victor1533111/SorterBot/CODIGO/Imagenes/angulo.jpg

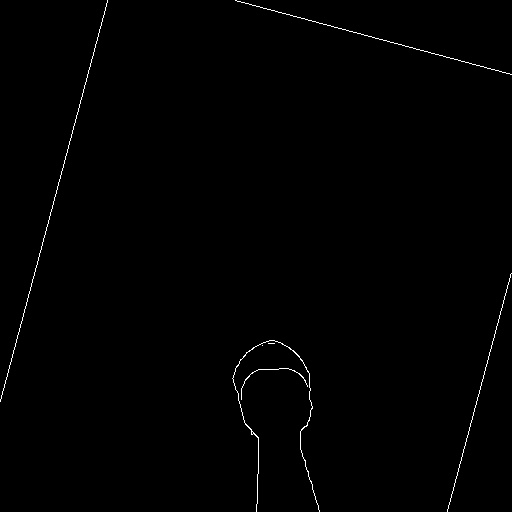
CODIGO/Imagenes/angulo.jpg
