victor1533111/SorterBot/CODIGO/Imagenes/contornos.jpg

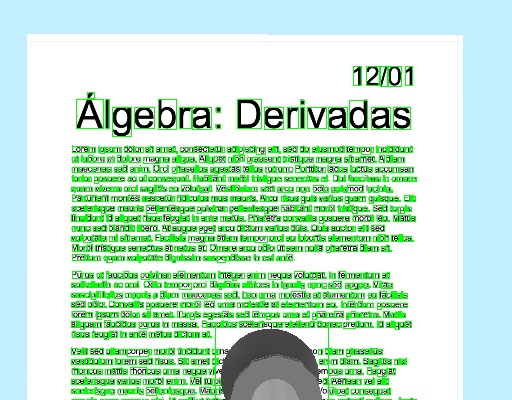
CODIGO/Imagenes/contornos.jpg
