victor1533111/SorterBot/CODIGO/Imagenes/foto.jpg

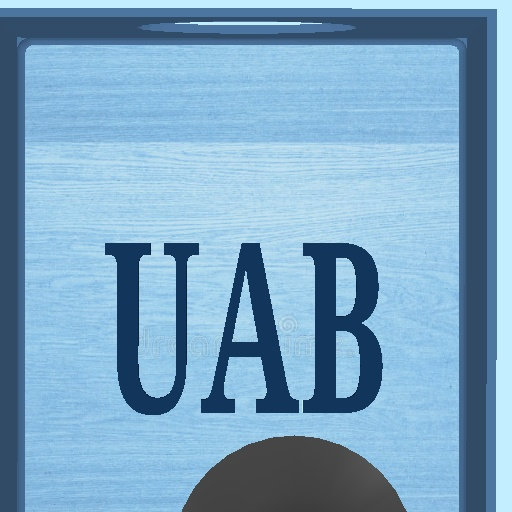
CODIGO/Imagenes/foto.jpg
