victor1533111/SorterBot/CODIGO/Imagenes/foto_titulo.jpg

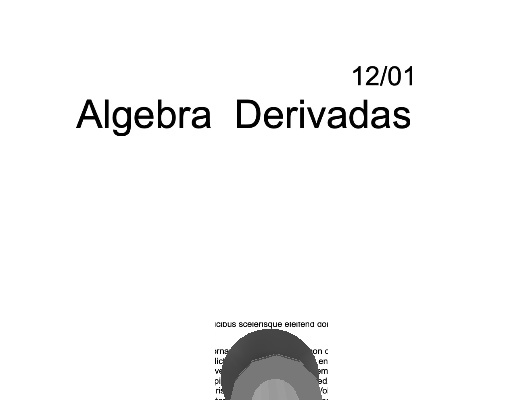
CODIGO/Imagenes/foto_titulo.jpg
