victor1533111/SorterBot/COMPONENTES/TEXTURAS/Colores/0c4315f0d65723472475a9147a5b7592.jpg

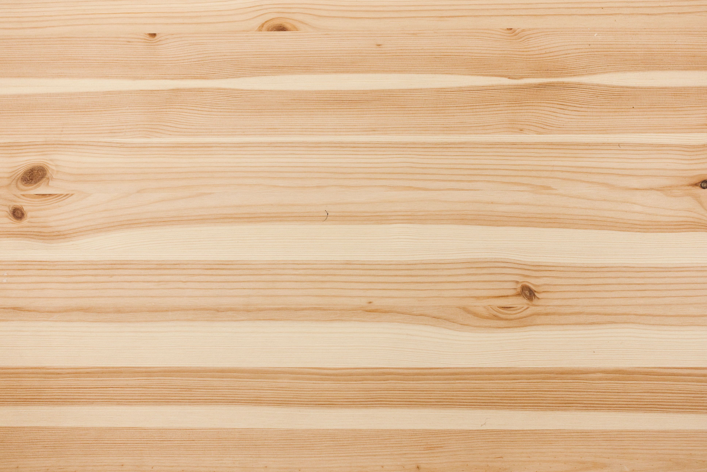
COMPONENTES/TEXTURAS/Colores/0c4315f0d65723472475a9147a5b7592.jpg
