victor1533111/SorterBot/COMPONENTES/TEXTURAS/Colores/40899414-suelo-de-parqué-gris-textura-de-madera-con-tablones-horizontales.jpg

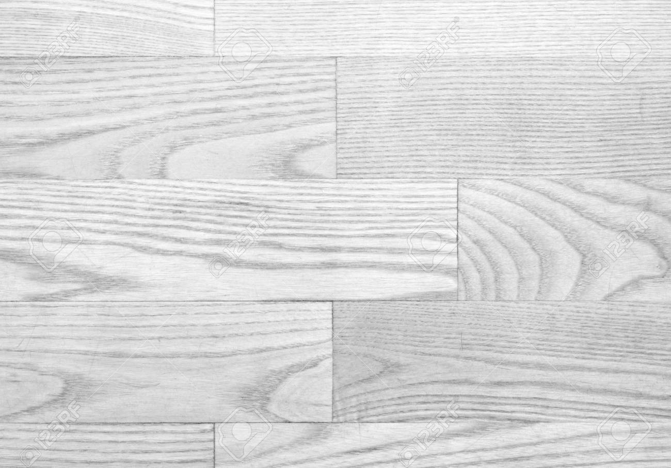
COMPONENTES/TEXTURAS/Colores/40899414-suelo-de-parqué-gris-textura-de-madera-con-tablones-horizontales.jpg
