victor1533111/SorterBot/COMPONENTES/TEXTURAS/Colores/cropped-uab.jpg

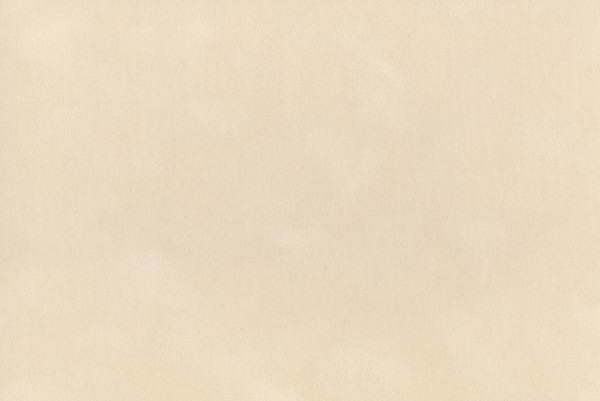
COMPONENTES/TEXTURAS/Colores/cropped-uab.jpg
