victor1533111/SorterBot/COMPONENTES/TEXTURAS/Colores/depositphotos_195791748-stock-photo-dark-brown-scratched-wooden-cutting.png

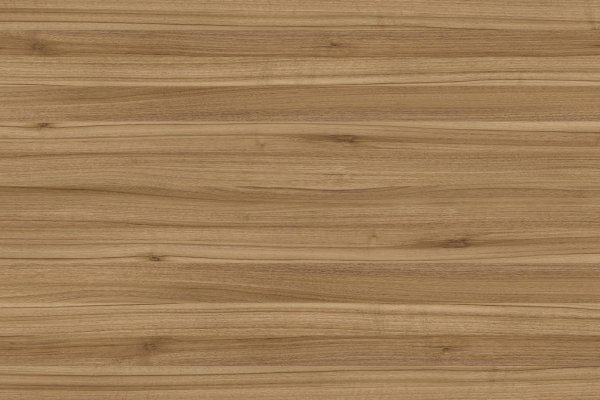
COMPONENTES/TEXTURAS/Colores/depositphotos_195791748-stock-photo-dark-brown-scratched-wooden-cutting.png
