victor1533111/SorterBot/COMPONENTES/TEXTURAS/Colores/fondo-de-textura-suelo-laminado-blanco-inoxidable-parqué-madera-gris-pulida-168998200.jpg

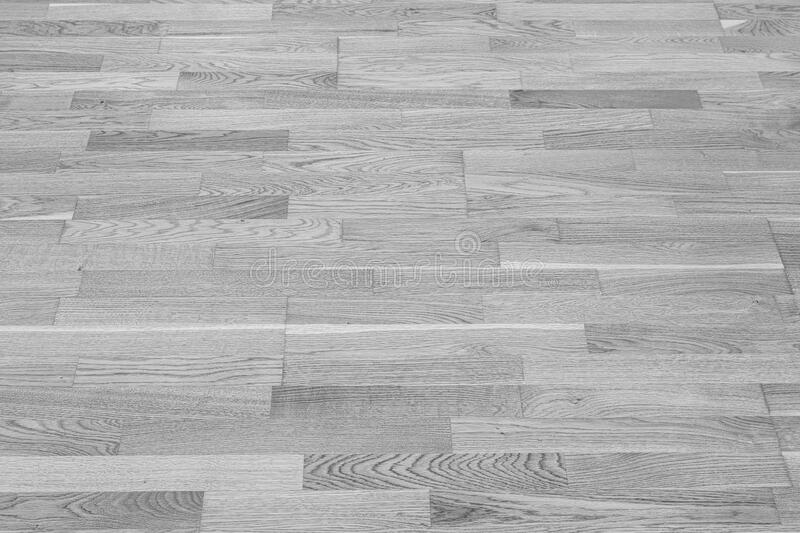
COMPONENTES/TEXTURAS/Colores/fondo-de-textura-suelo-laminado-blanco-inoxidable-parqué-madera-gris-pulida-168998200.jpg
