victor1533111/SorterBot/COMPONENTES/TEXTURAS/Colores/fp_eiche_no1102_1199010840_sb_of1223_plan_191213_1.jpg

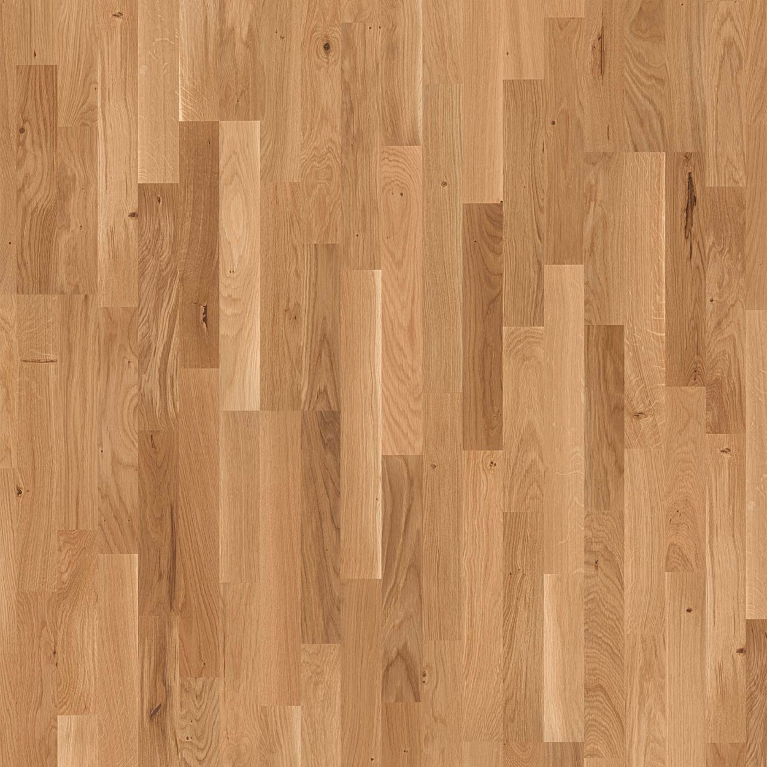
COMPONENTES/TEXTURAS/Colores/fp_eiche_no1102_1199010840_sb_of1223_plan_191213_1.jpg
