victor1533111/SorterBot/COMPONENTES/TEXTURAS/Colores/imu1861_1.jpg

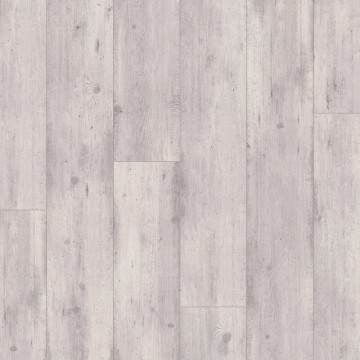
COMPONENTES/TEXTURAS/Colores/imu1861_1.jpg
