victor1533111/SorterBot/COMPONENTES/TEXTURAS/Colores/parquet.png

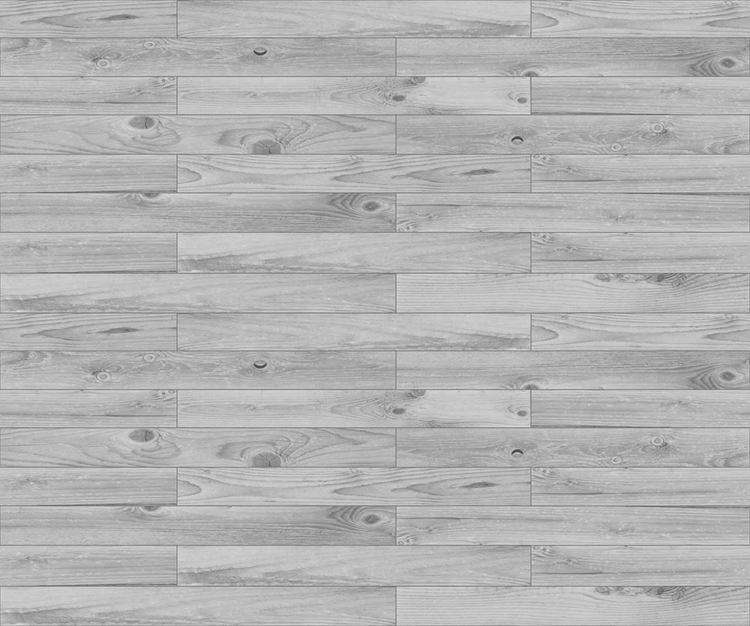
COMPONENTES/TEXTURAS/Colores/parquet.png
