victor1533111/SorterBot/COMPONENTES/TEXTURAS/Colores/wood-texture-table-top-surface-background-natural-pattern-top-view-wood-texture-table-top-surface-ba.png

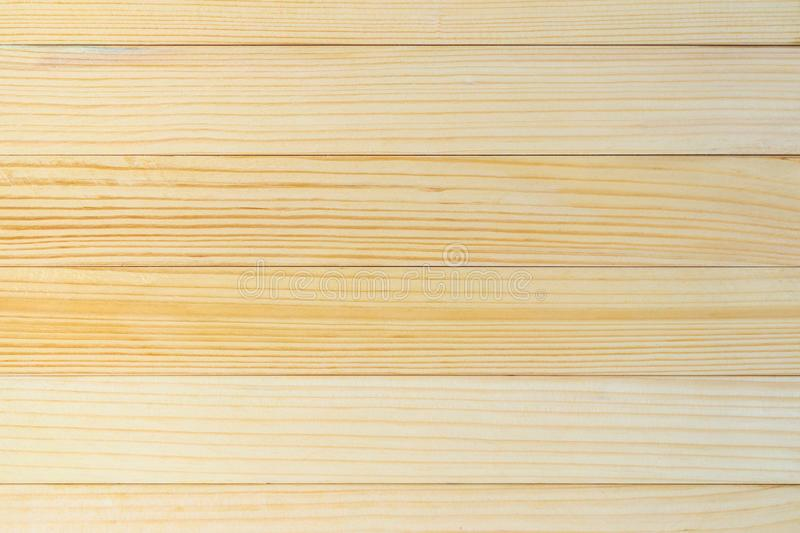
COMPONENTES/TEXTURAS/Colores/wood-texture-table-top-surface-background-natural-pattern-top-view-wood-texture-table-top-surface-ba.png
