victor1533111/SorterBot/COMPONENTES/TEXTURAS/Hojas/AC_Processador.jpg

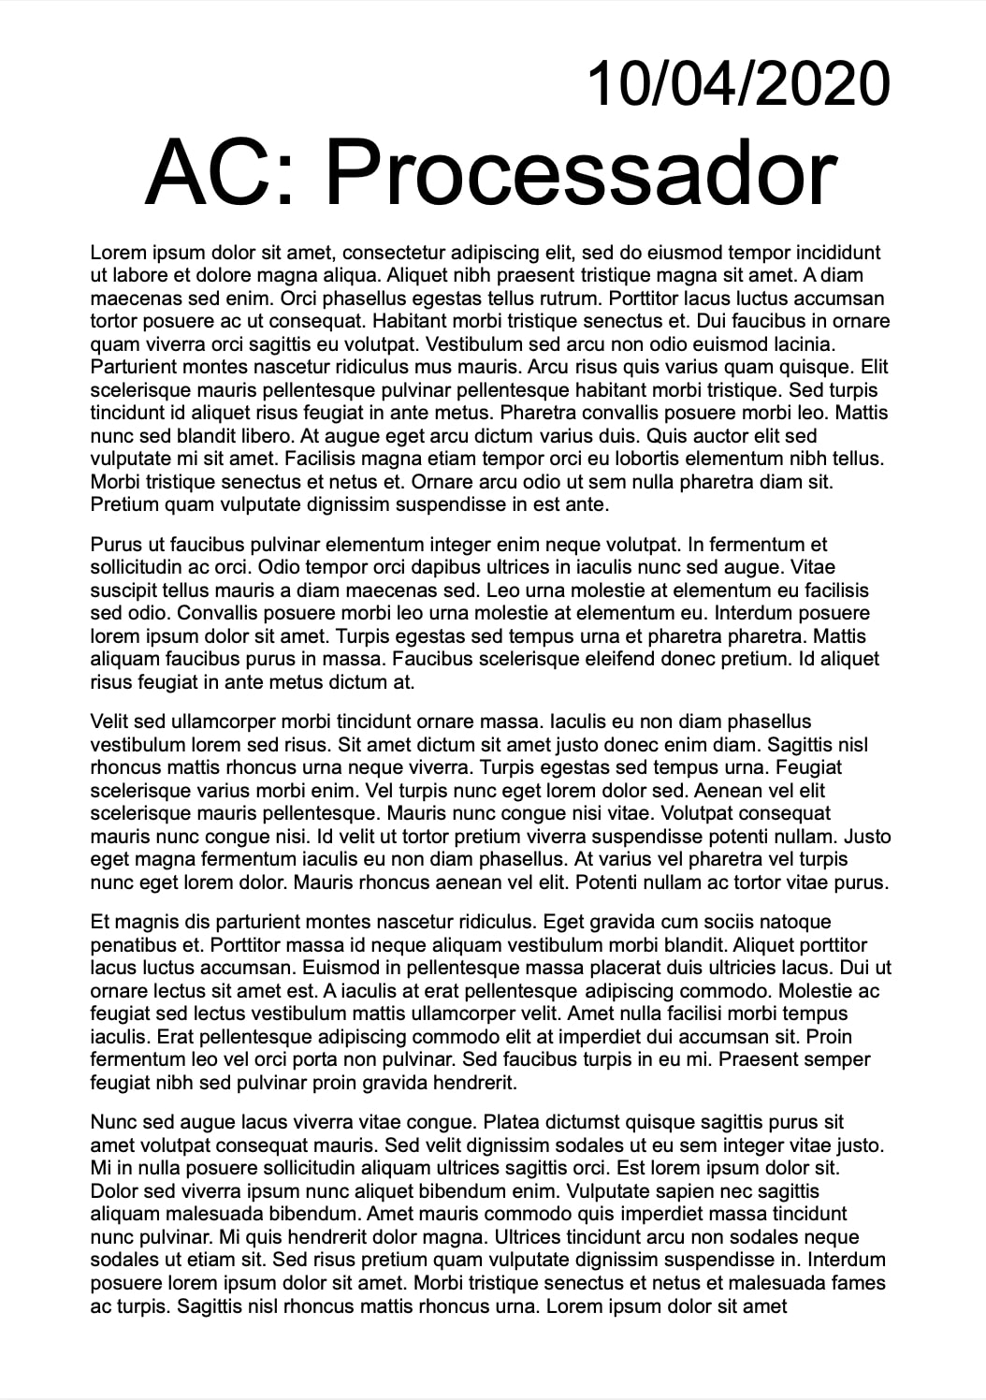
COMPONENTES/TEXTURAS/Hojas/AC_Processador.jpg
