victor1533111/SorterBot/COMPONENTES/TEXTURAS/Hojas/AC_SIMD.jpg

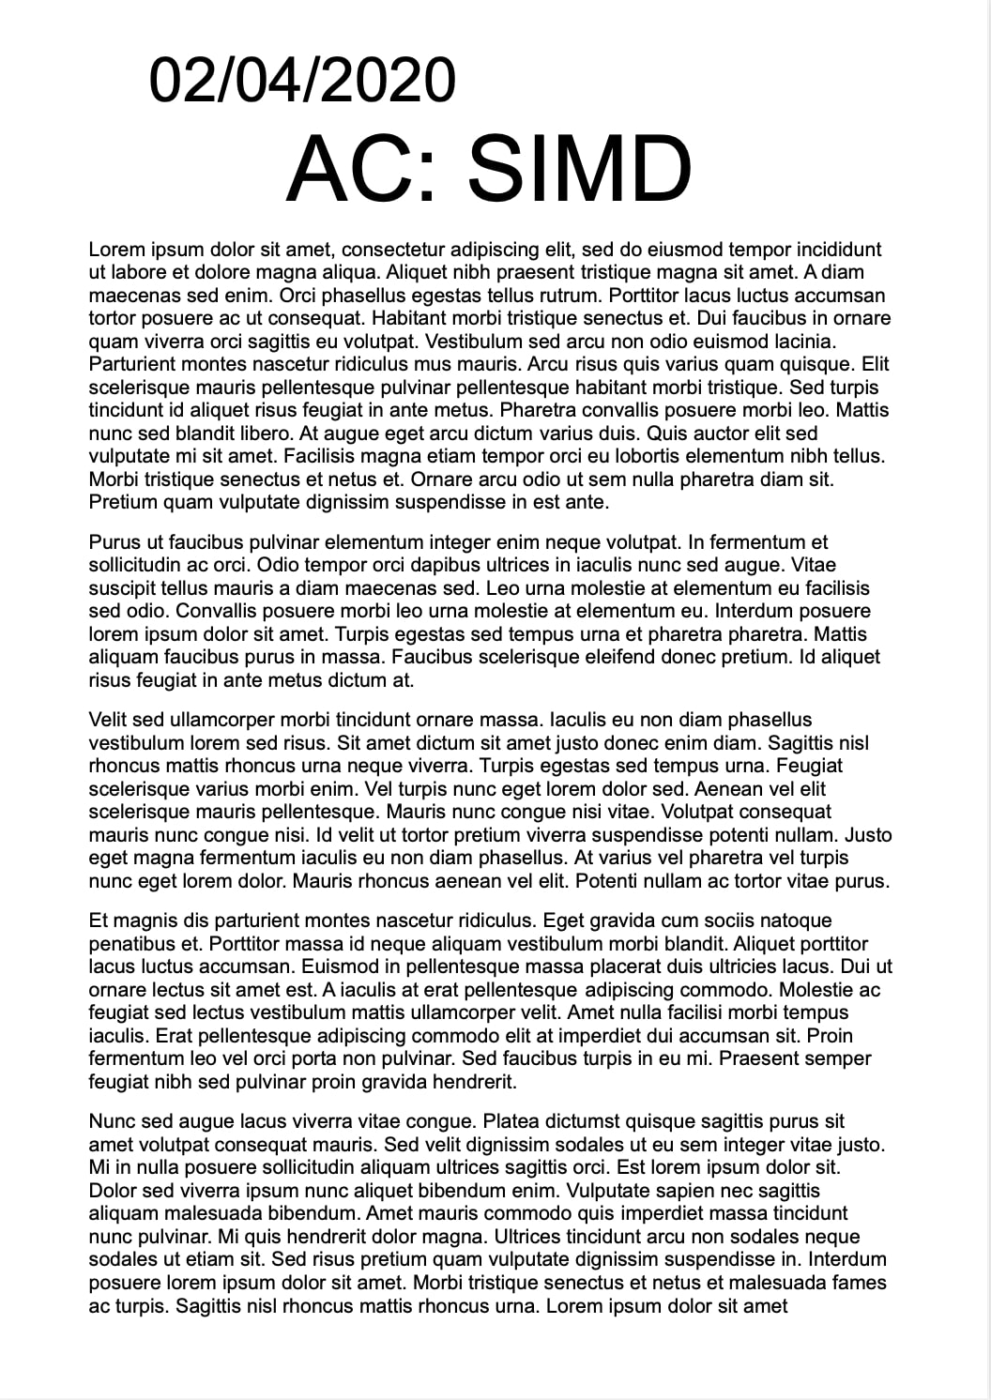
COMPONENTES/TEXTURAS/Hojas/AC_SIMD.jpg
