victor1533111/SorterBot/COMPONENTES/TEXTURAS/Hojas/Algebra_Derivadas.jpg

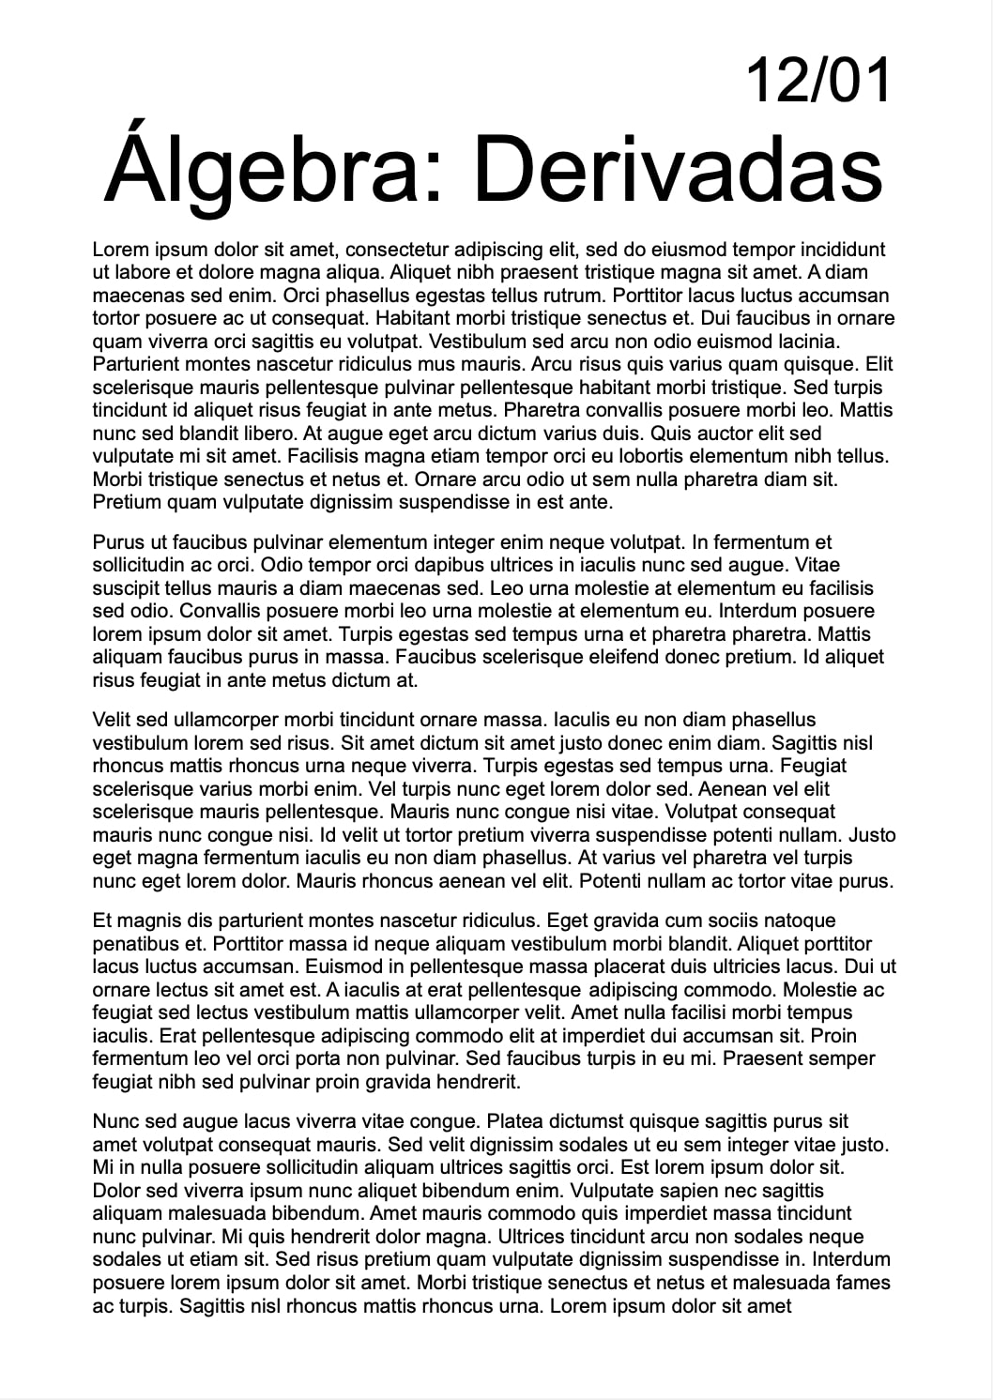
COMPONENTES/TEXTURAS/Hojas/Algebra_Derivadas.jpg
