victor1533111/SorterBot/COMPONENTES/TEXTURAS/Hojas/Algebra_Integrales.jpg

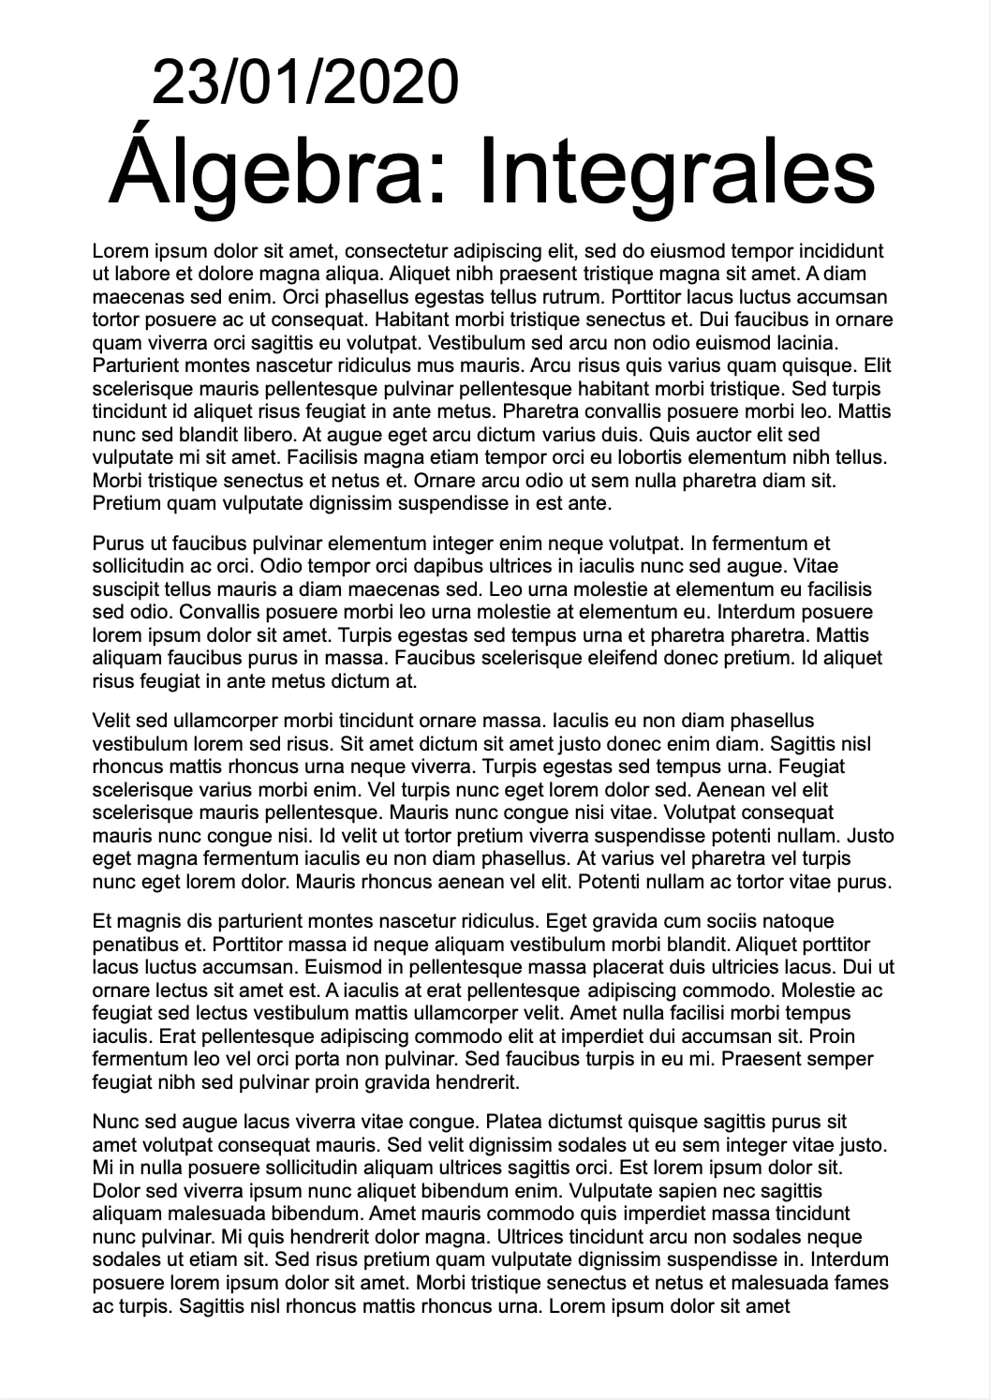
COMPONENTES/TEXTURAS/Hojas/Algebra_Integrales.jpg
