victor1533111/SorterBot/COMPONENTES/TEXTURAS/Hojas/Algebra_Matrices.jpg

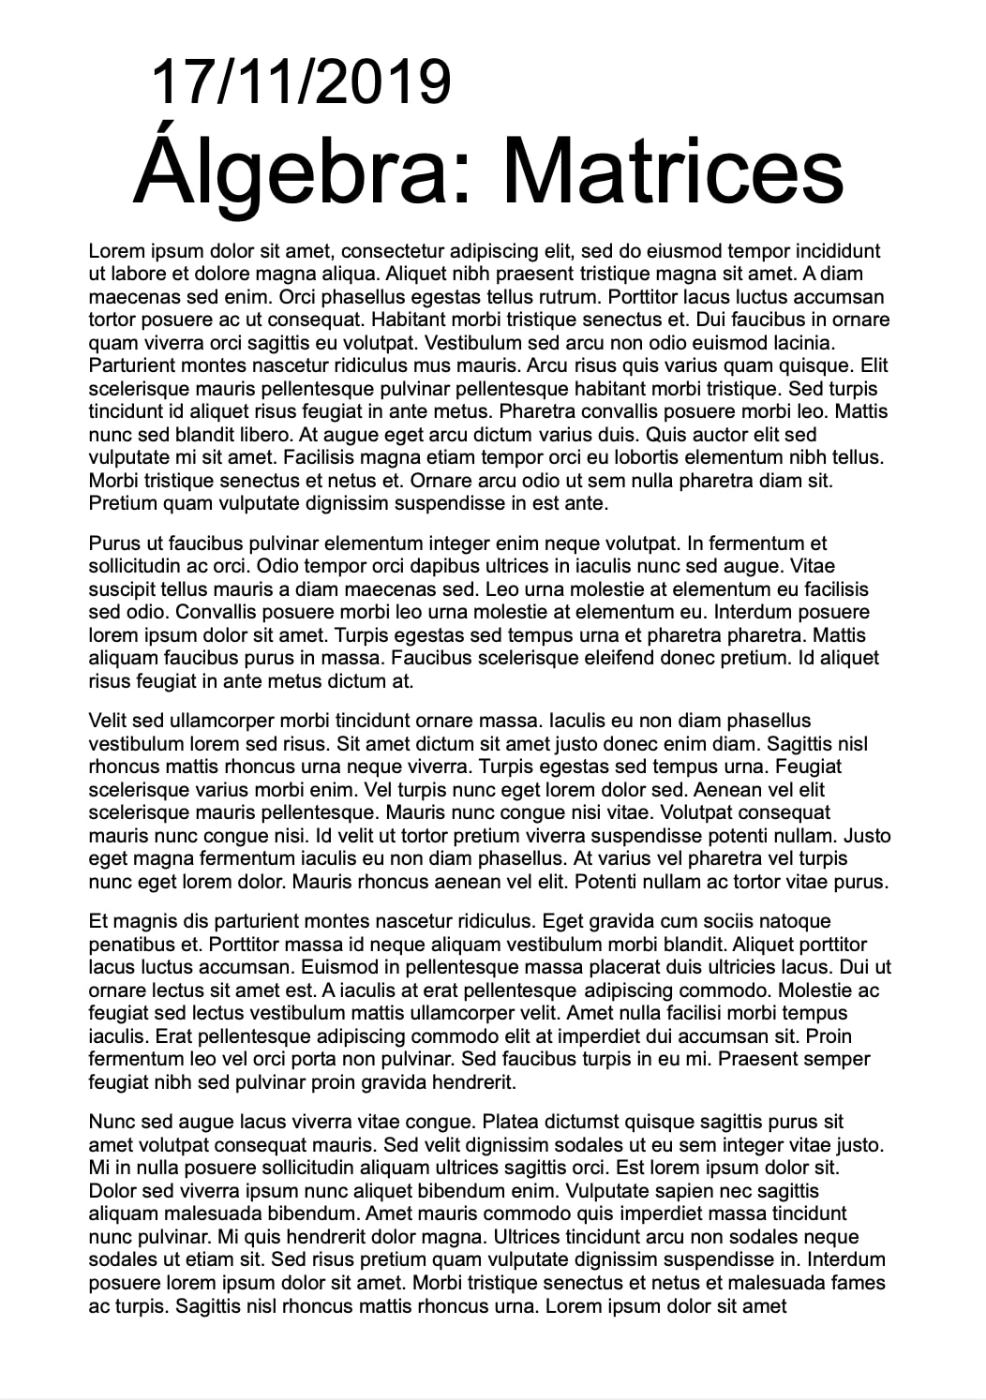
COMPONENTES/TEXTURAS/Hojas/Algebra_Matrices.jpg
