victor1533111/SorterBot/COMPONENTES/TEXTURAS/Hojas/Robotica_Algoritmo.jpg

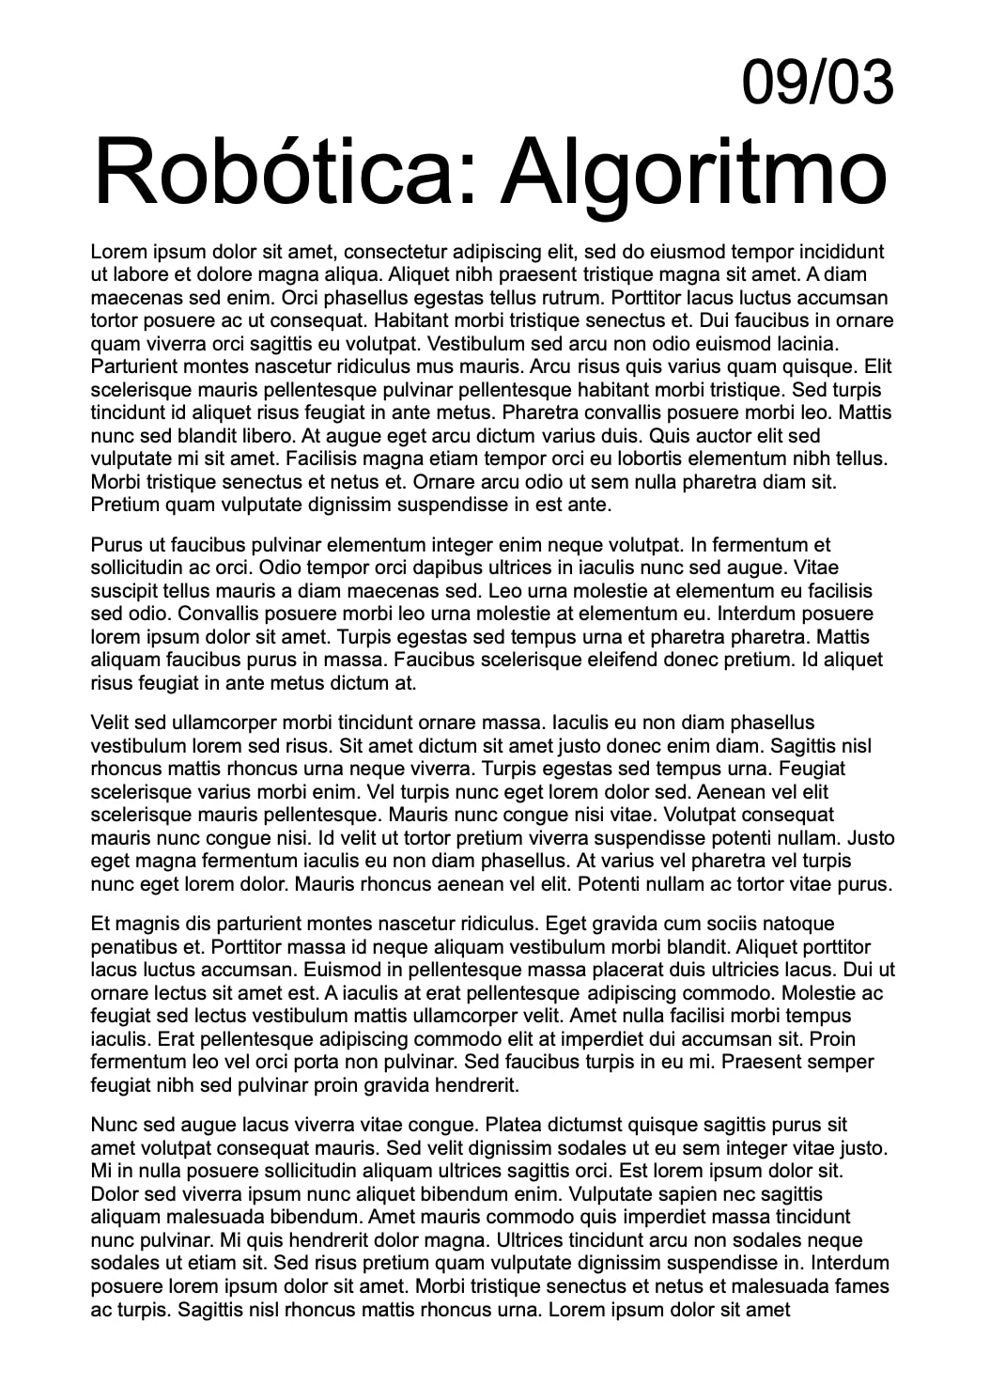
COMPONENTES/TEXTURAS/Hojas/Robotica_Algoritmo.jpg
