victor1533111/SorterBot/COMPONENTES/TEXTURAS/Hojas/Robotica_Cinematica.jpg

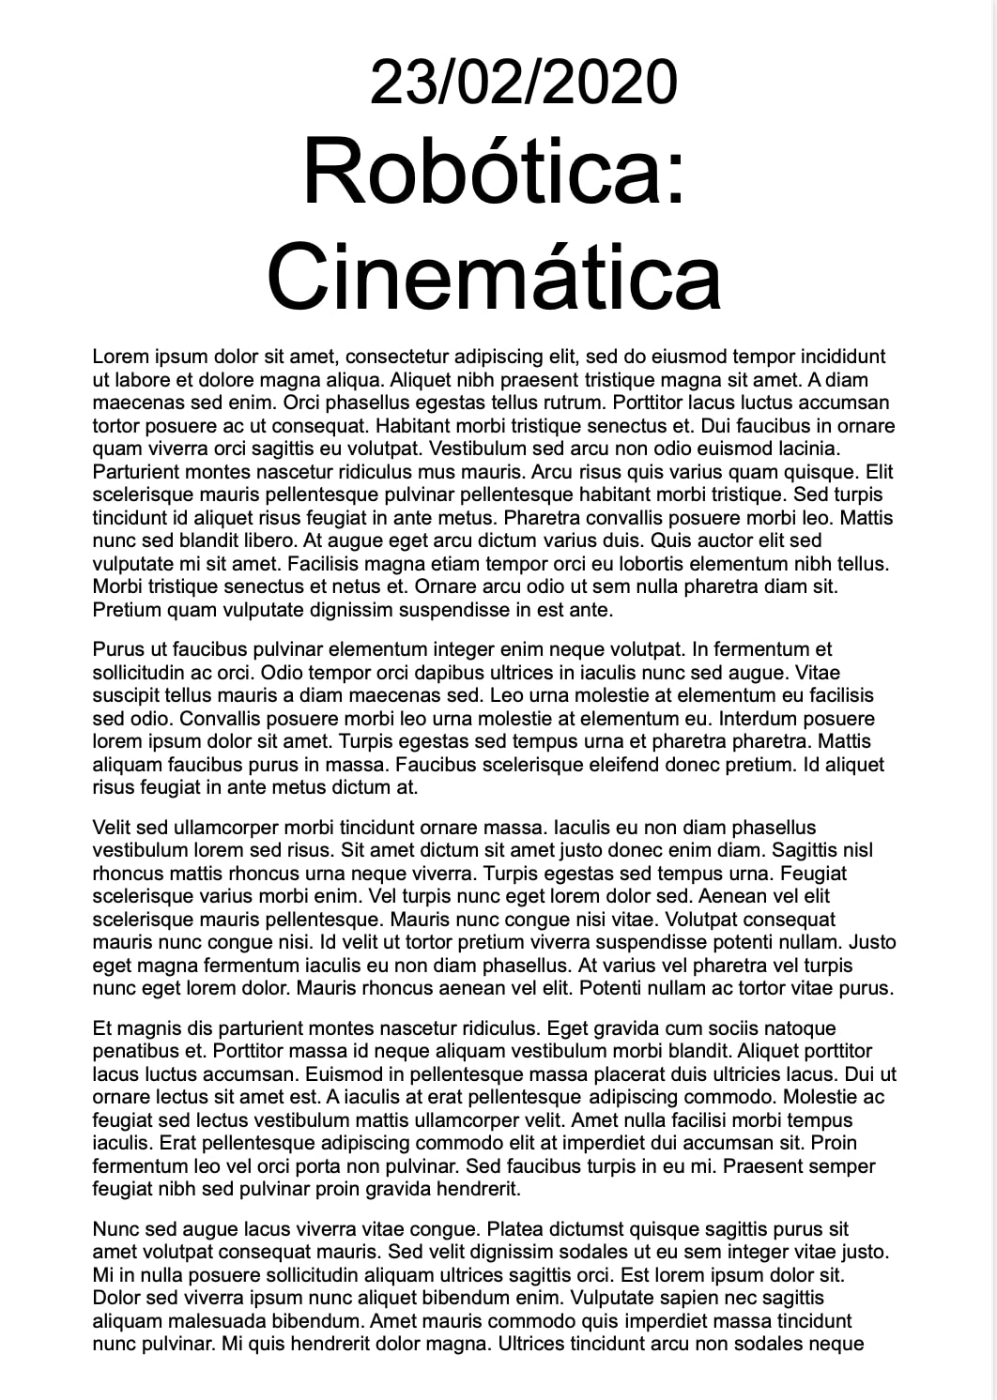
COMPONENTES/TEXTURAS/Hojas/Robotica_Cinematica.jpg
