victor1533111/SorterBot/COMPONENTES/TEXTURAS/Hojas/SO_Linux.jpg

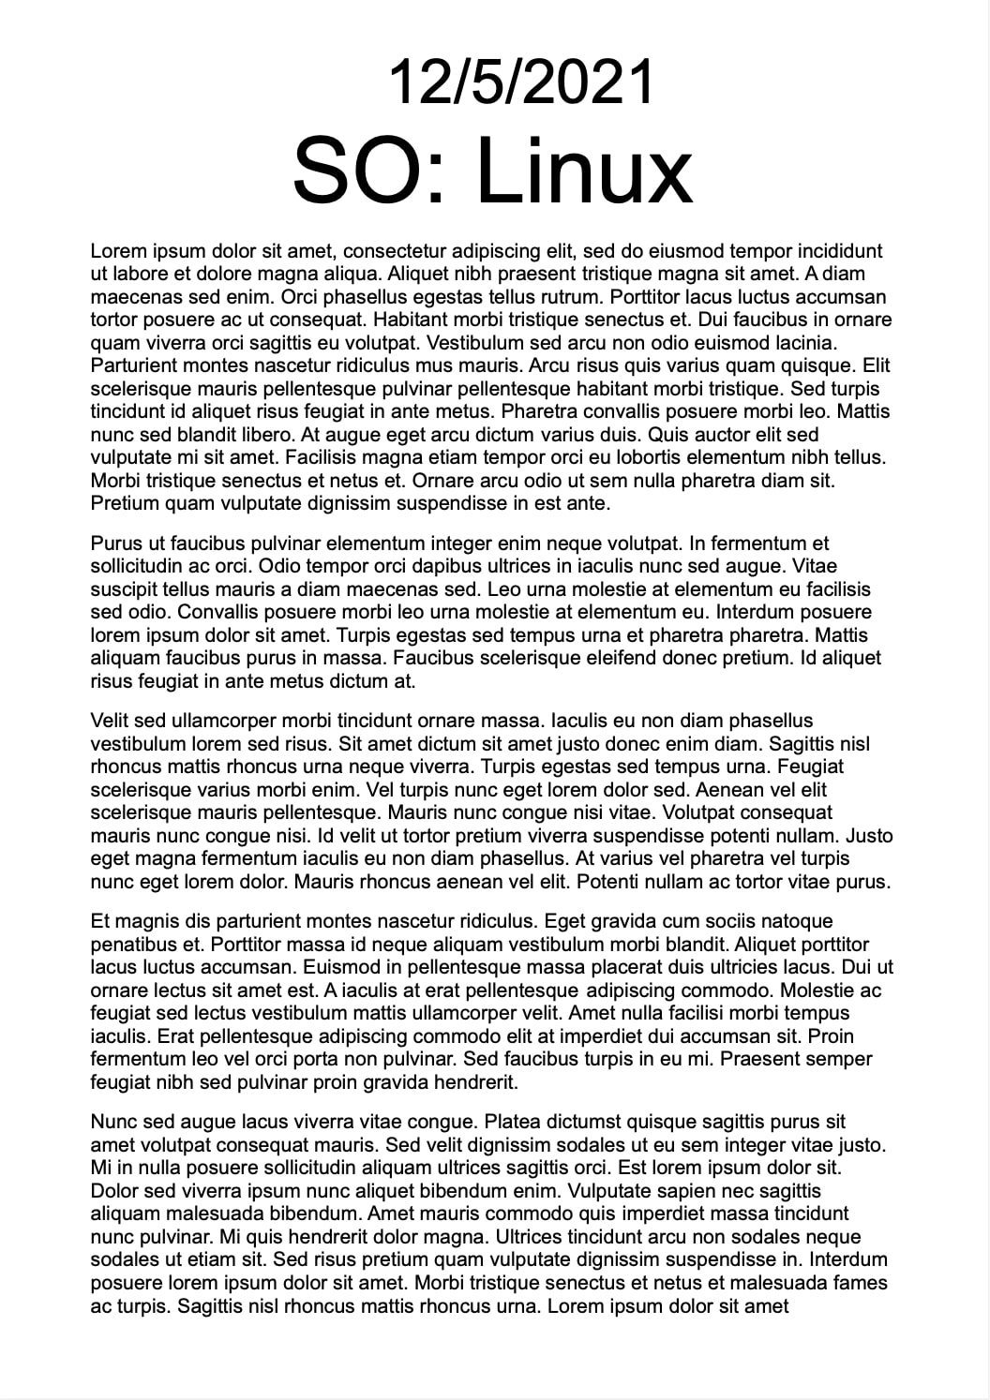
COMPONENTES/TEXTURAS/Hojas/SO_Linux.jpg
