victor1533111/SorterBot/COMPONENTES/TEXTURAS/Hojas/TDIW_CSS.jpg

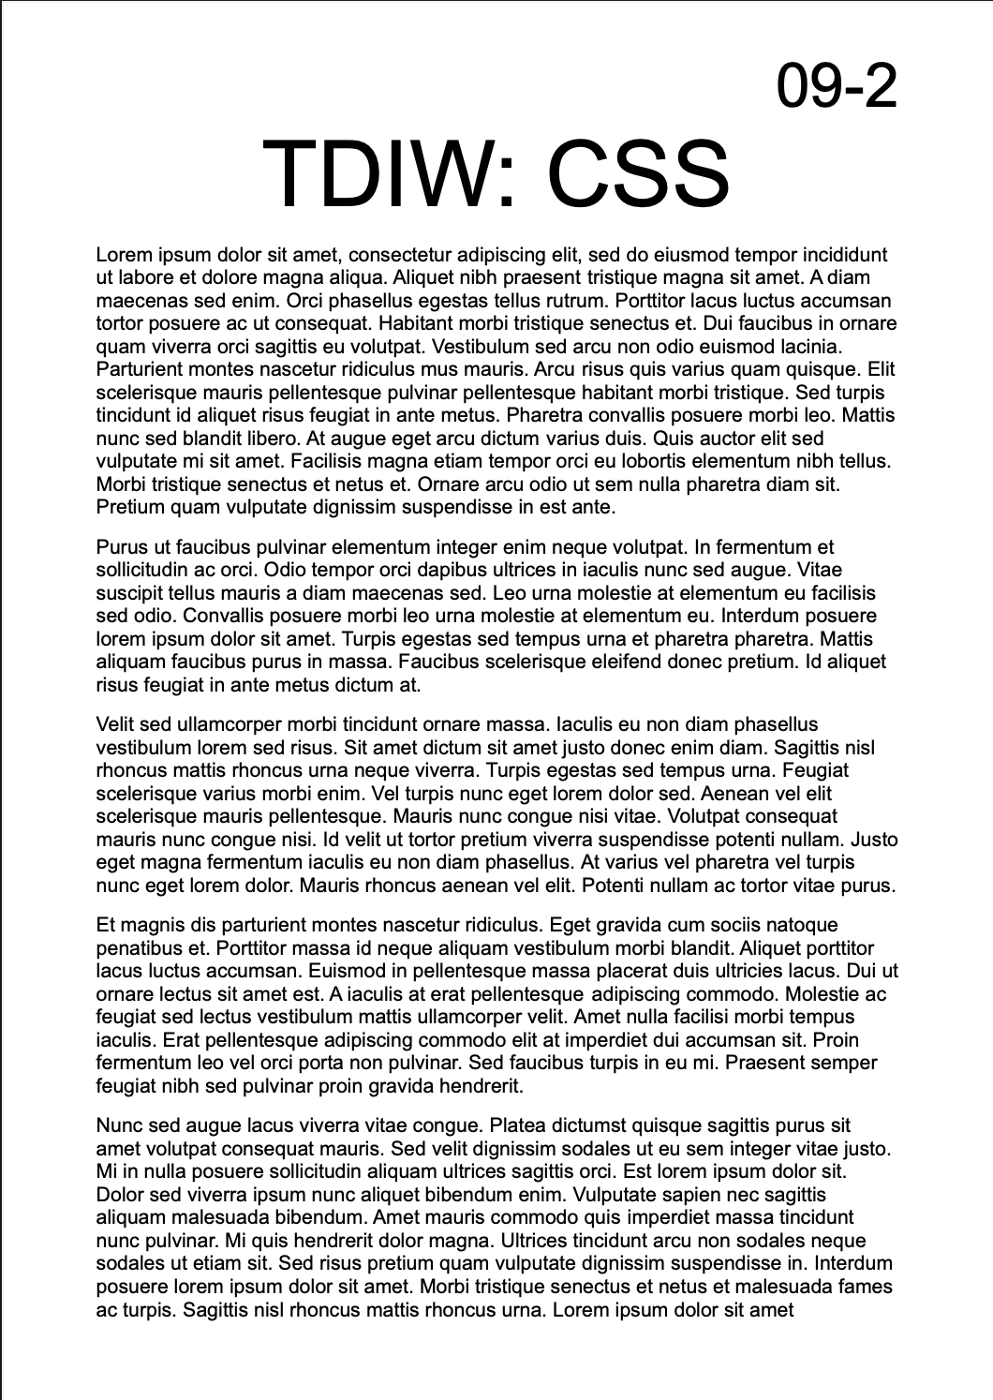
COMPONENTES/TEXTURAS/Hojas/TDIW_CSS.jpg
