victor1533111/SorterBot/COMPONENTES/TEXTURAS/Hojas/TDIW_JS.jpg

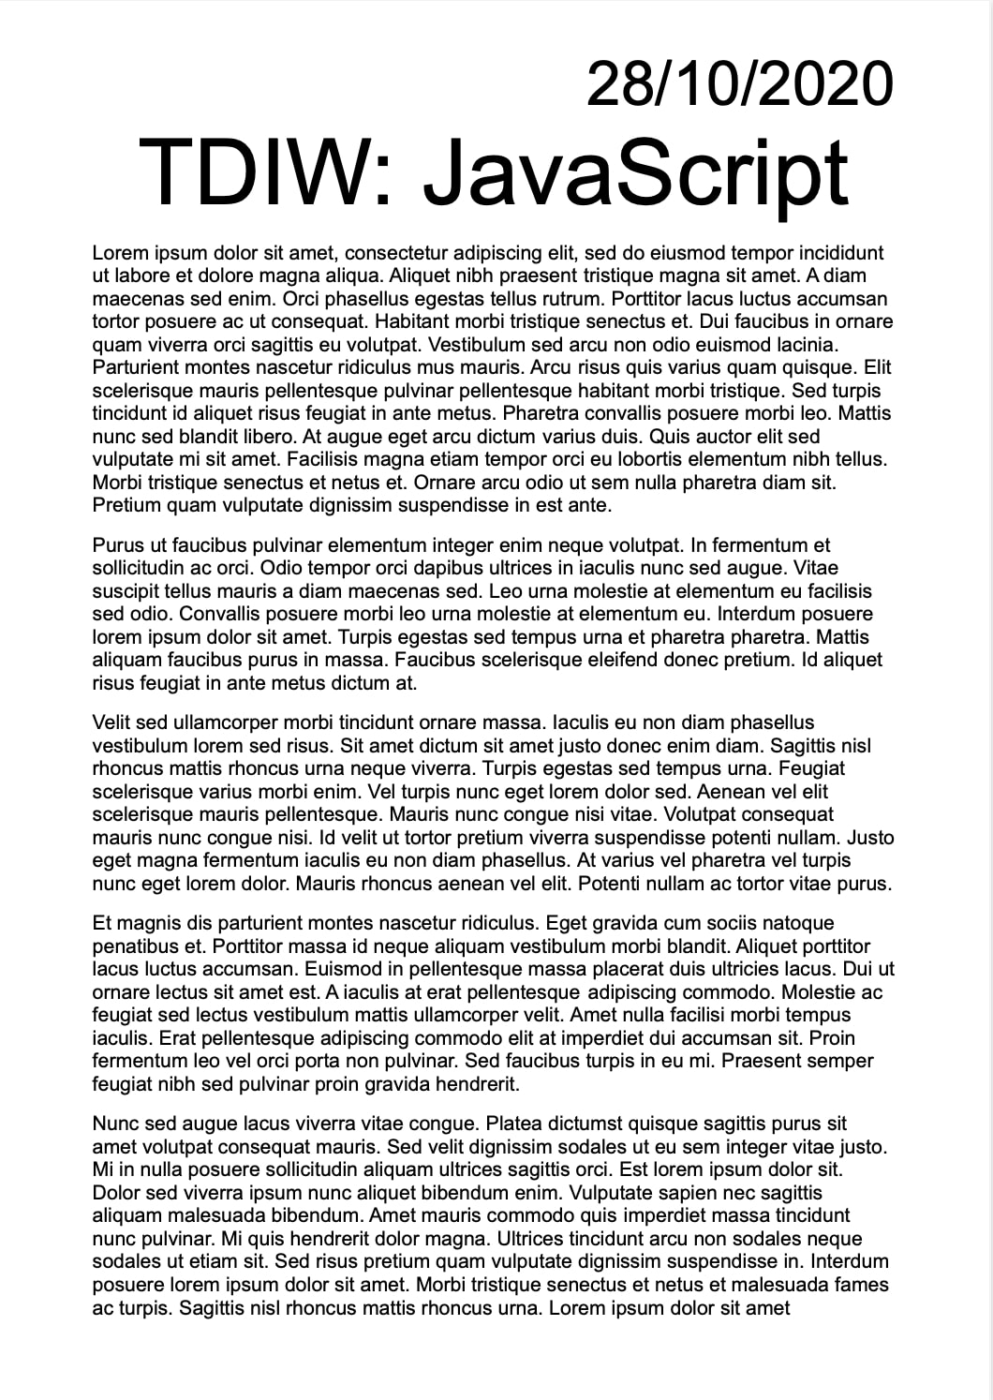
COMPONENTES/TEXTURAS/Hojas/TDIW_JS.jpg
