victor1533111/SorterBot/COMPONENTES/TEXTURAS/Hojas/TDIW_PHP.jpg

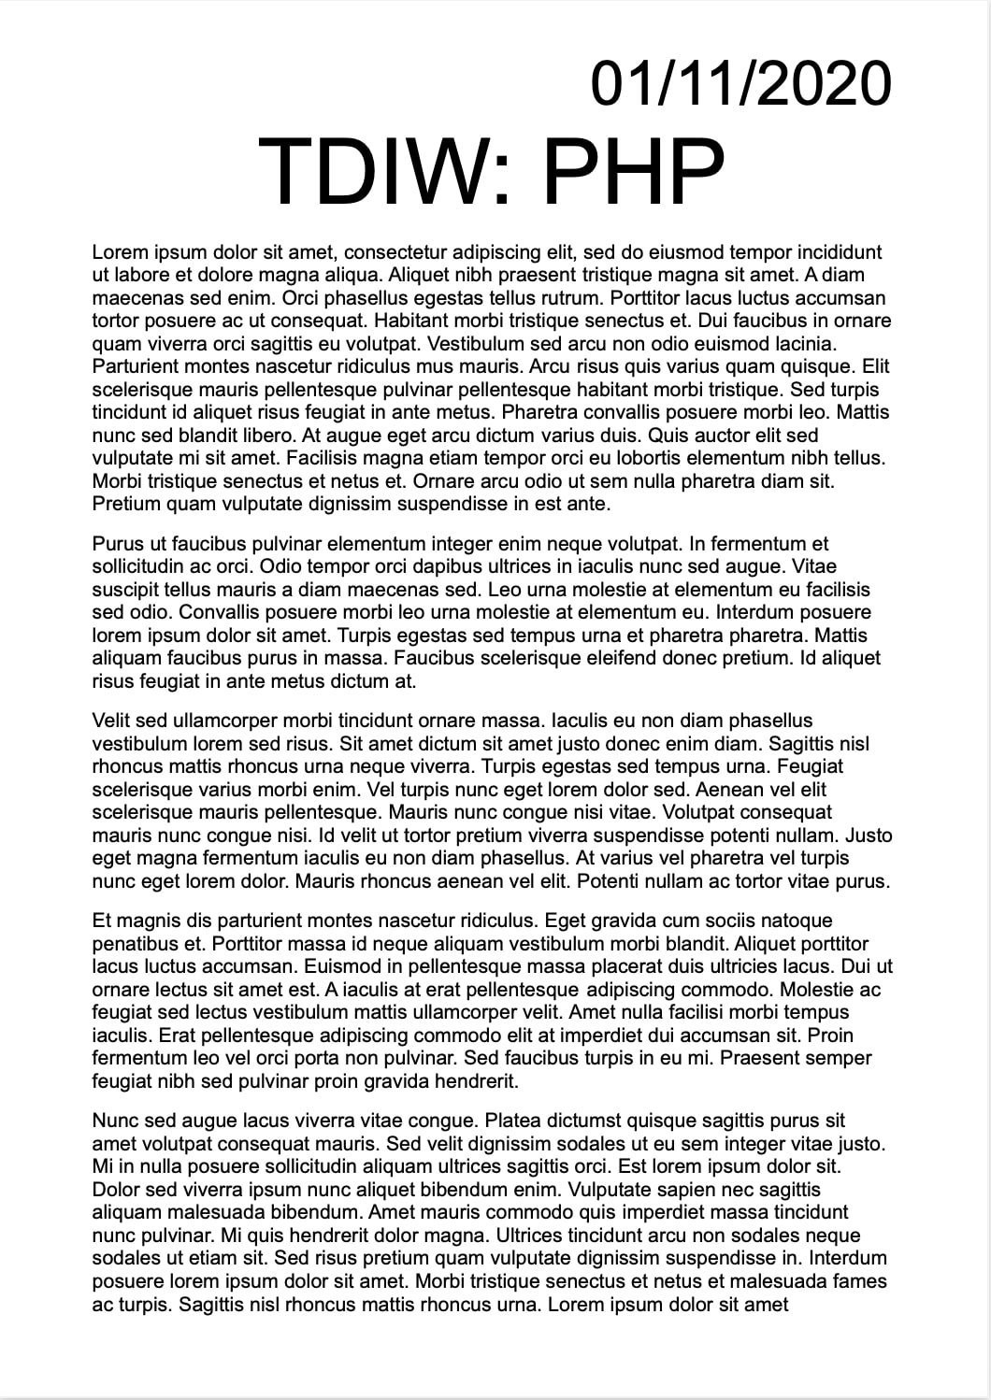
COMPONENTES/TEXTURAS/Hojas/TDIW_PHP.jpg
