victor1533111/SorterBot/COMPONENTES/TEXTURAS/Hojas/vc.PNG

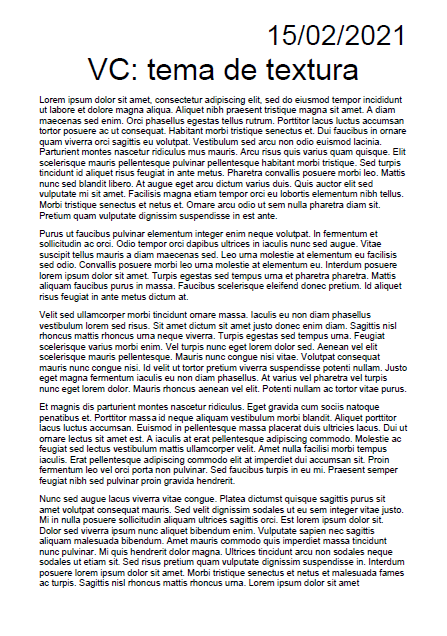
COMPONENTES/TEXTURAS/Hojas/vc.PNG
