victor1533111/SorterBot/COMPONENTES/TEXTURAS/Hojas/VC_reconocimiento.jpg

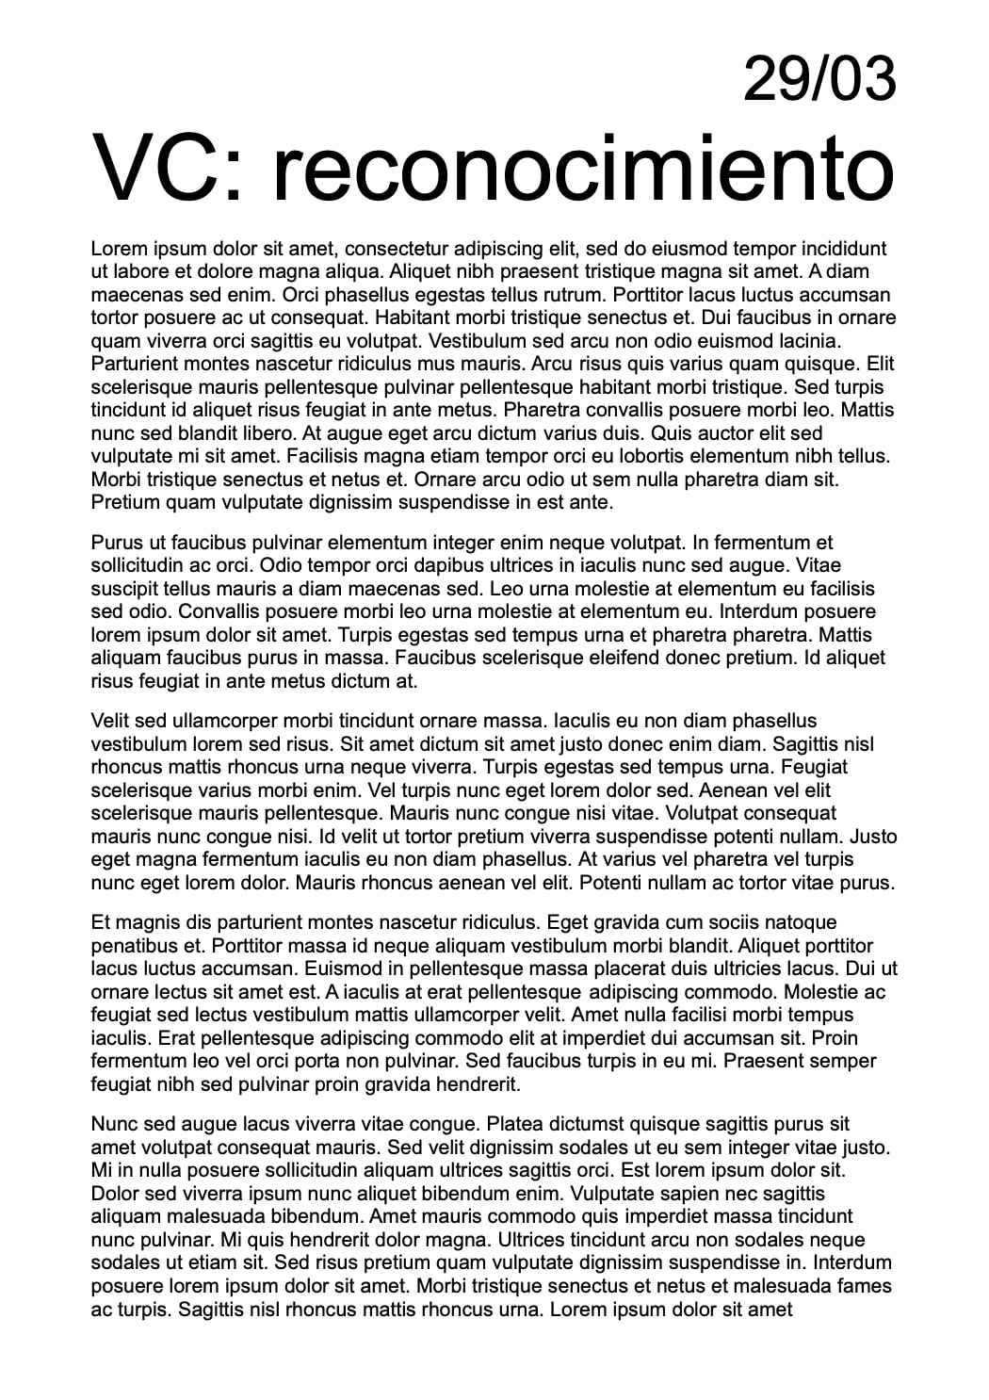
COMPONENTES/TEXTURAS/Hojas/VC_reconocimiento.jpg
