victor1533111/SorterBot/COMPONENTES/TEXTURAS/Hojas/VC_Segmentacion.jpg

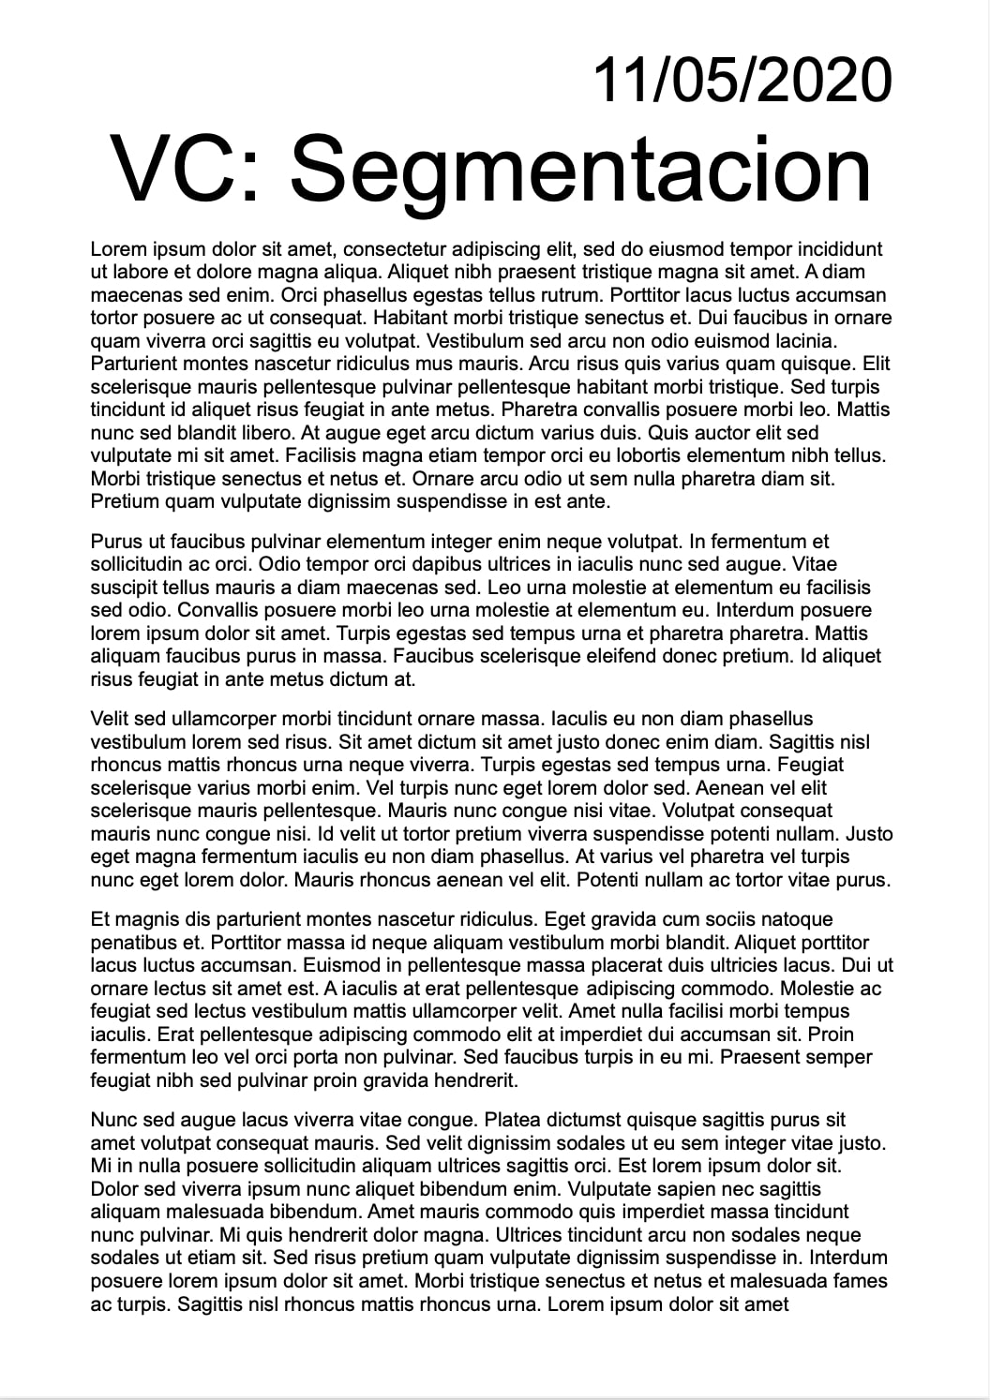
COMPONENTES/TEXTURAS/Hojas/VC_Segmentacion.jpg
