victor1533111/SorterBot/COMPONENTES/TEXTURAS/Hojas/VGI_GABBOR.PNG

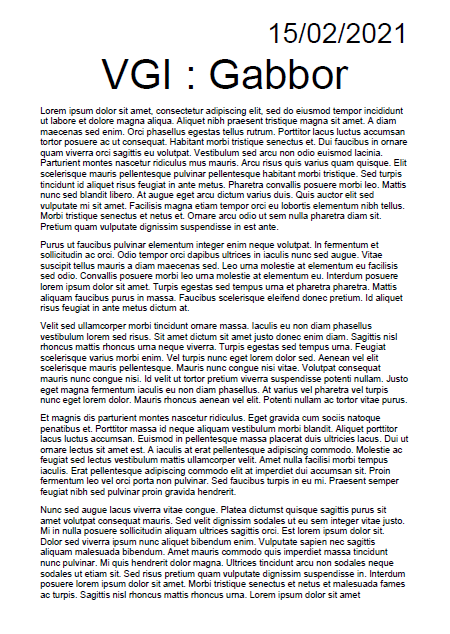
COMPONENTES/TEXTURAS/Hojas/VGI_GABBOR.PNG
