victor1533111/SorterBot/COMPONENTES/TEXTURAS/Hojas/VGI_LUCES.PNG

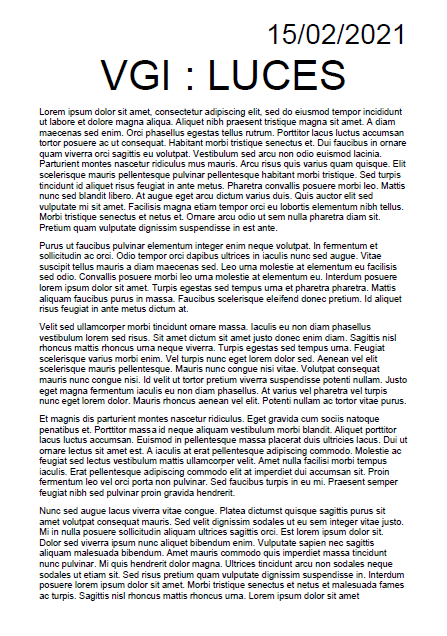
COMPONENTES/TEXTURAS/Hojas/VGI_LUCES.PNG
