victor1533111/SorterBot/COMPONENTES/MTL/Mesa.obj

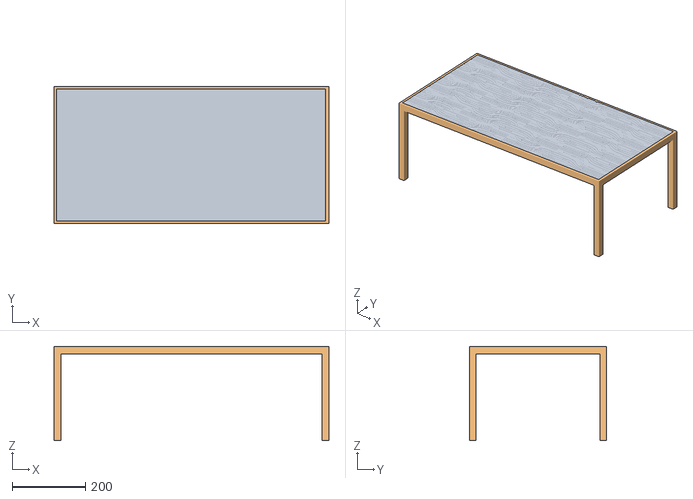
[picture p61: CAD file, 2021-05-19]
COMPONENTES/MTL/Mesa.obj
751.5 x 375.0 x 258.2
