victor1533111/SorterBot/COMPONENTES/MTL/Brazo_Rotacional.obj

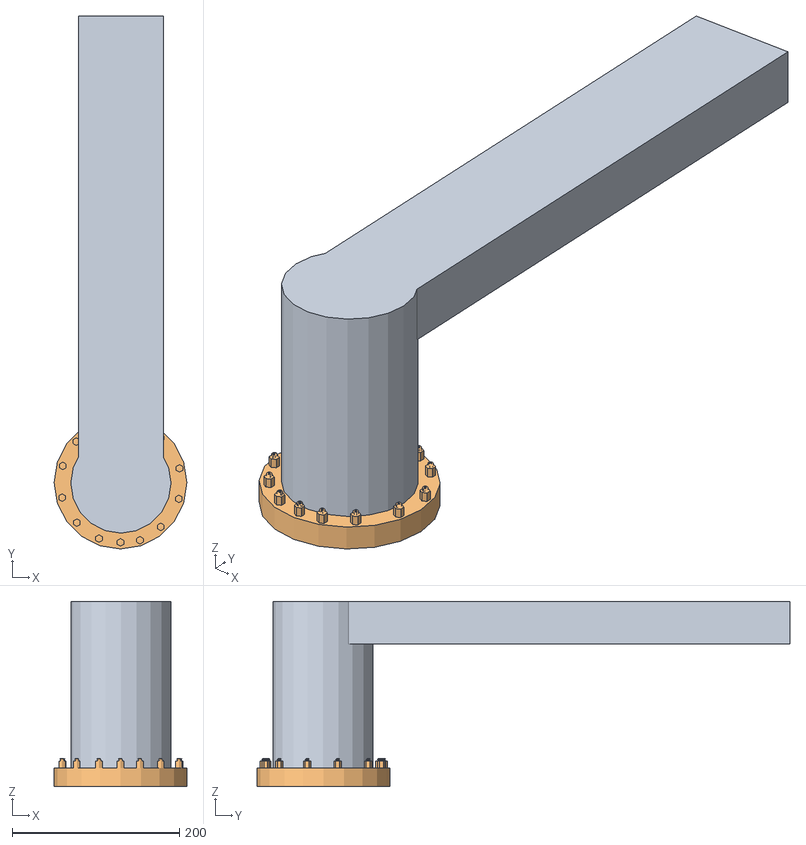
[picture p62: CAD file, 2021-05-19]
COMPONENTES/MTL/Brazo_Rotacional.obj
159.0 x 638.0 x 222.0
